DagaVedant/NotGoingToBeLateToSchool/firmware/globe.h

/*
  32x32 spinning globe, 24 frames, 1 bit per pixel, 4 bytes per row.
  same animation as the oled on my hackpad, reused here on the tft.
  format matches Adafruit_GFX drawBitmap() so it can be drawn directly.
*/

#pragma once

#define GLOBE_FRAMES 24
#define GLOBE_SIZE 32

static const uint8_t PROGMEM globe[GLOBE_FRAMES][GLOBE_SIZE * 4] = {
    {0x00, 0x00, 0x00, 0x00, 0x00, 0x0F, 0xF0, 0x00, 0x00, 0x78, 0x1E, 0x00, 0x01, 0xF6, 0x0F, 0x80, 0x03, 0x2C, 0x0F, 0xC0, 0x07, 0x90, 0x7F, 0xE0, 0x0F, 0x80, 0x5F, 0xF0, 0x1E, 0x01, 0x7F, 0xF8, 0x18, 0x01, 0xFF, 0xF8, 0x30, 0x00, 0xF9, 0xFC, 0x20, 0x03, 0xBF, 0xFC, 0x20, 0x03, 0x01, 0xFC, 0x60, 0x03, 0xE3, 0xE6, 0x40, 0x03, 0xFF, 0xF6, 0x40, 0x07, 0xFF, 0xE2, 0x60, 0x0F, 0xFF, 0xE2, 0x70, 0x0F, 0xFF, 0xC2, 0x70, 0x0F, 0xFF, 0xE2, 0x78, 0x07, 0xFF, 0xE2, 0x78, 0x07, 0xFF, 0xC6, 0x3E, 0x00, 0x3F, 0x84, 0x3F, 0x00, 0x3F, 0x84, 0x3F, 0x00, 0x1F, 0x8C, 0x1E, 0x00, 0x1F, 0x88, 0x1E, 0x00, 0x1F, 0x58, 0x0C, 0x00, 0x1E, 0x30, 0x06, 0x00, 0x1C, 0x60, 0x03, 0x00, 0x08, 0xC0, 0x01, 0xC0, 0x03, 0x80, 0x00, 0x78, 0x1E, 0x00, 0x00, 0x0F, 0xF0, 0x00, 0x00, 0x00, 0x00, 0x00},
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
};
